elik745i/ESP-Pressure-Transducer/3D/3d_Models/cable-gland-18.snapshot.6/Screenshot 2024-12-11 at 10.22.05 AM.png

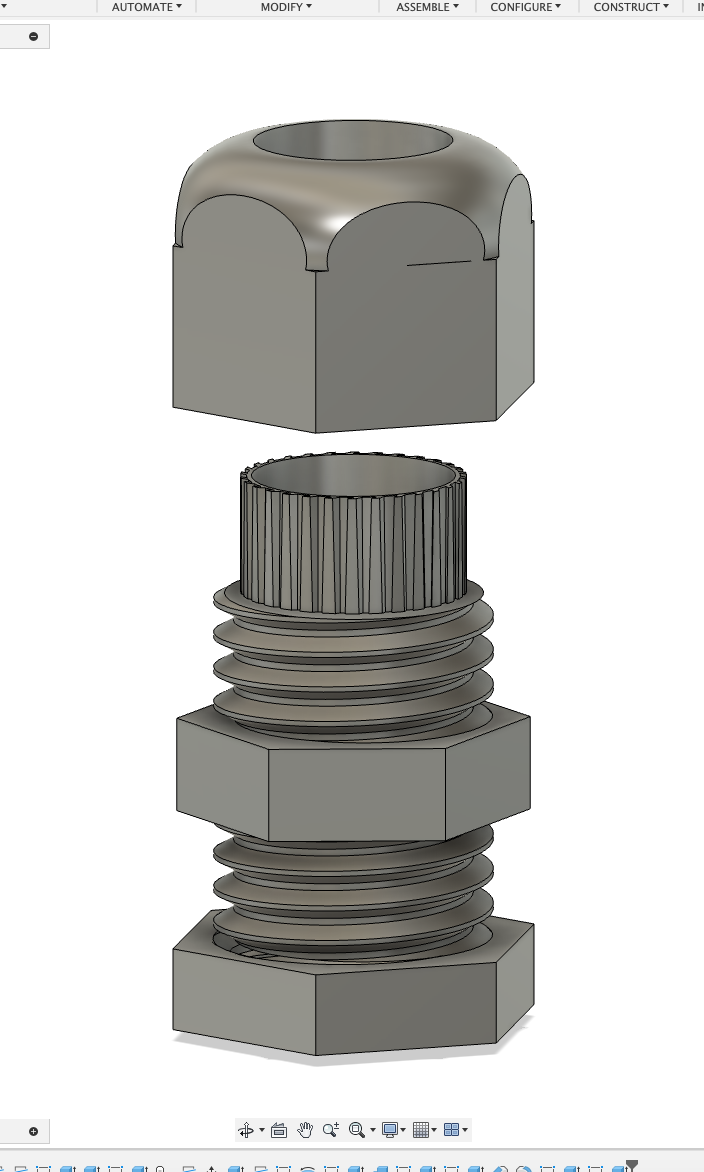
3D/3d_Models/cable-gland-18.snapshot.6/Screenshot 2024-12-11 at 10.22.05 AM.png
