elik745i/ESP-Pressure-Transducer/3D/3d_Models/mlh100pgb01a-transducer-1.snapshot.11/MLH100PGB01A.jpg

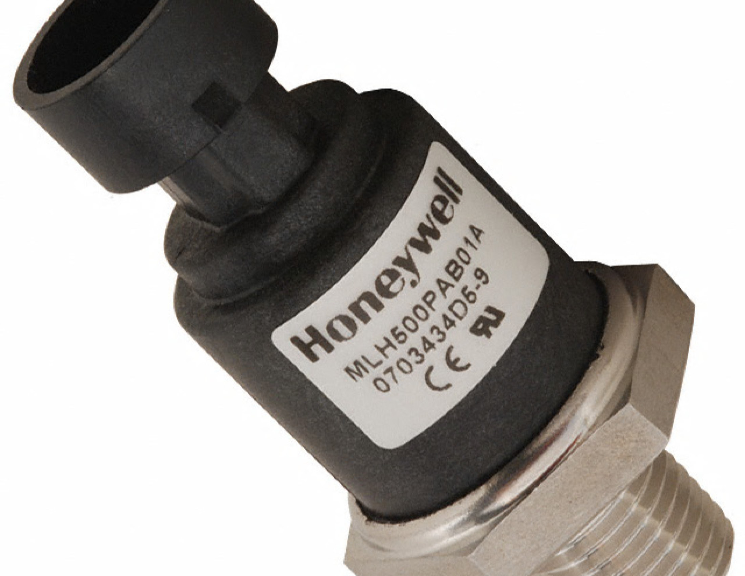
3D/3d_Models/mlh100pgb01a-transducer-1.snapshot.11/MLH100PGB01A.jpg
