elik745i/ESP-Pressure-Transducer/3D/3d_Models/polyamid-kablo-rakoru-polyamide-cable-gland-1.snapshot.6/2024-08-10_15-54-43.png

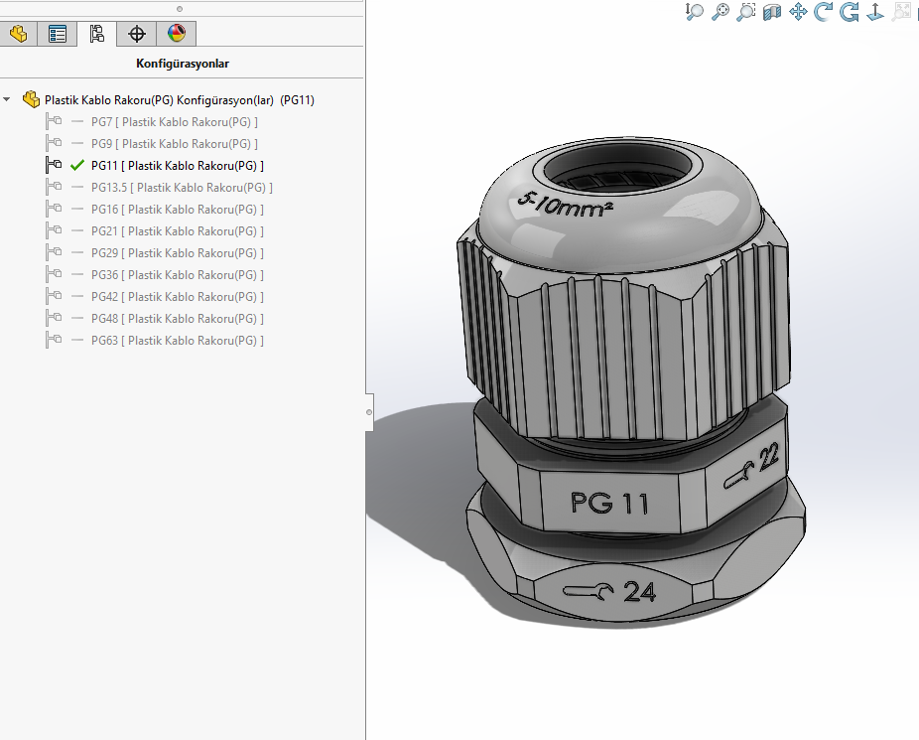
3D/3d_Models/polyamid-kablo-rakoru-polyamide-cable-gland-1.snapshot.6/2024-08-10_15-54-43.png
