elik745i/ESP-Pressure-Transducer/Docs/1.jpeg

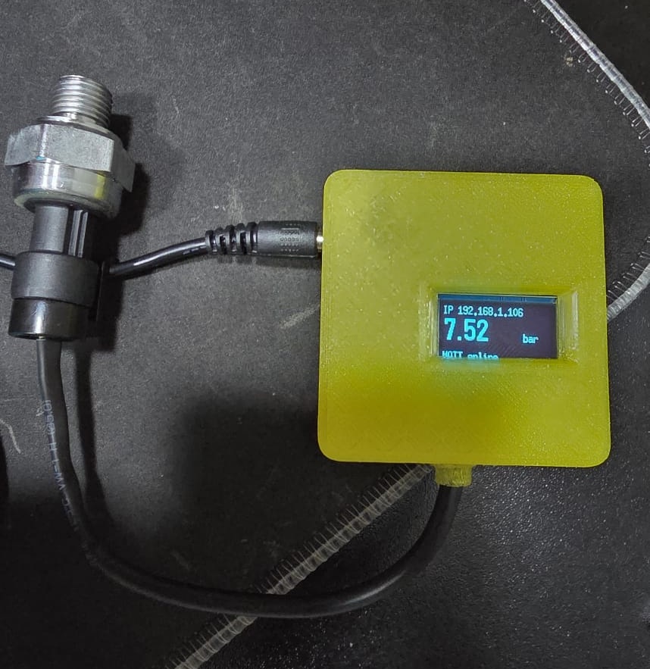
Docs/1.jpeg
