elik745i/ESP-Pressure-Transducer/Docs/2.jpeg

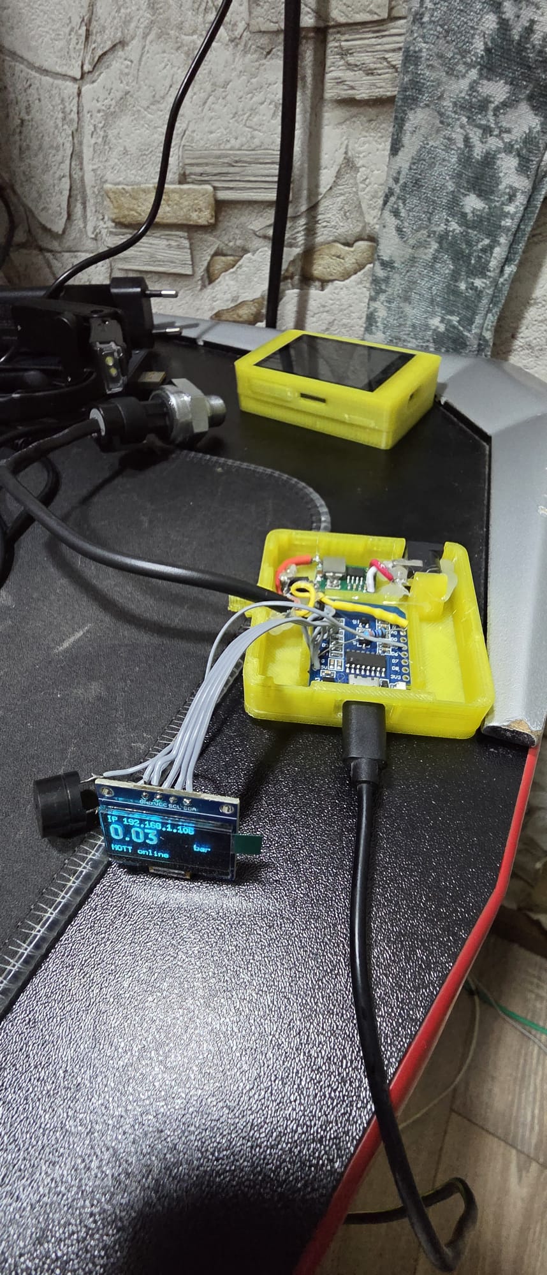
Docs/2.jpeg
