elik745i/ESP-Pressure-Transducer/Docs/3.jpeg

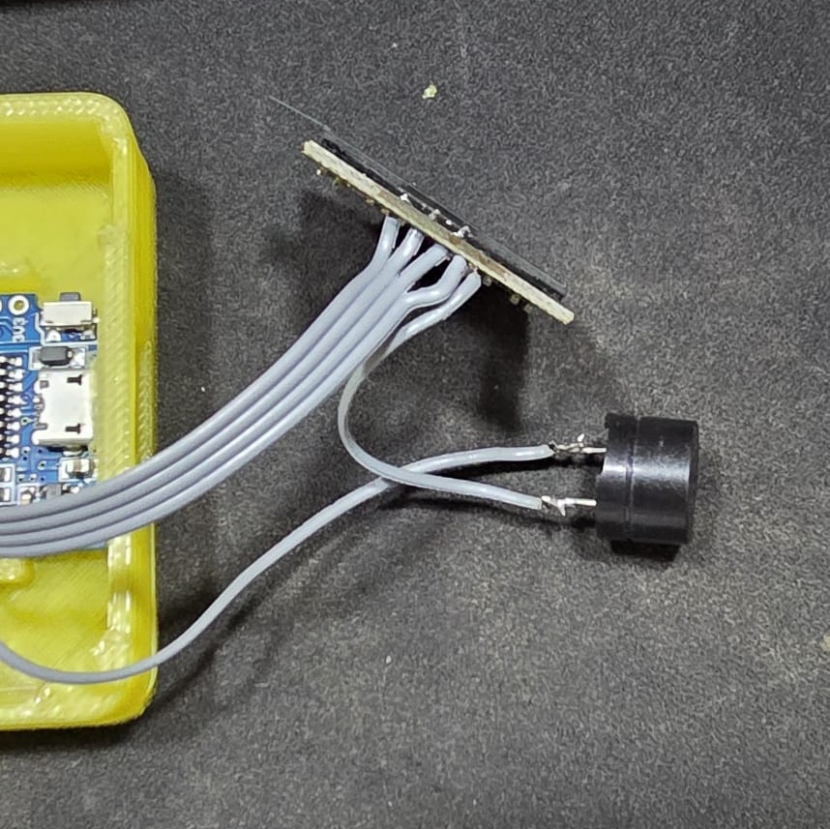
Docs/3.jpeg
