elik745i/ESP-Pressure-Transducer/Docs/4.jpeg

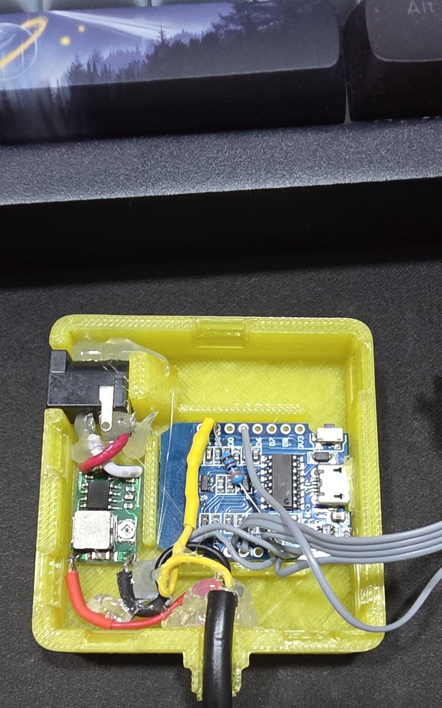
Docs/4.jpeg
