elik745i/ESP-Pressure-Transducer/Docs/botth sensors.jpg

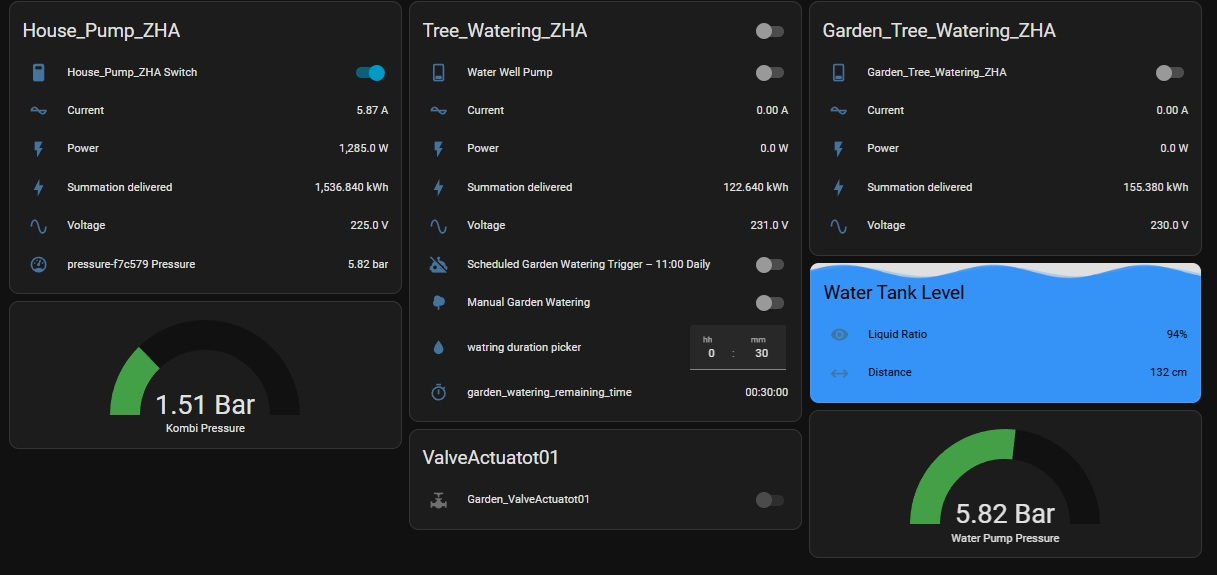
Docs/botth sensors.jpg
