elik745i/ESP-Pressure-Transducer/Docs/espo.jpeg

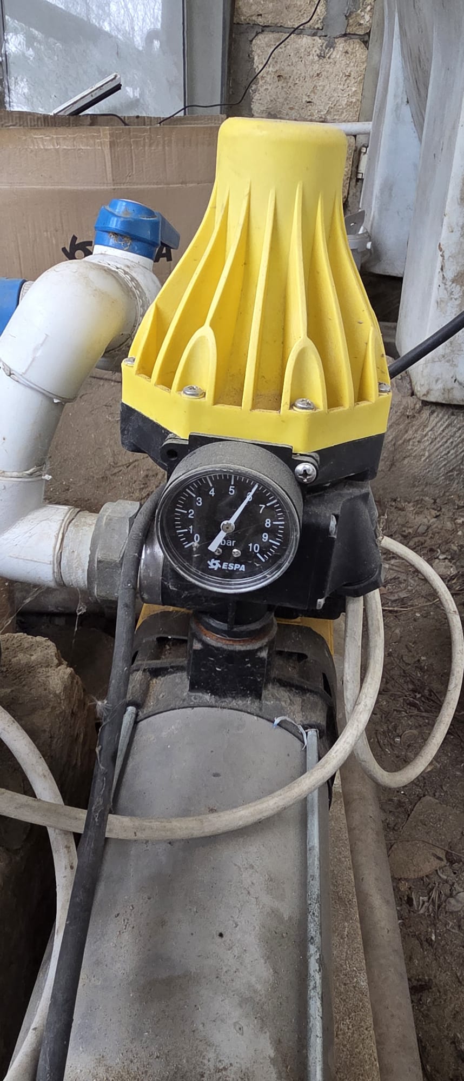
Docs/espo.jpeg
