elik745i/ESP-Pressure-Transducer/Docs/touch1.png

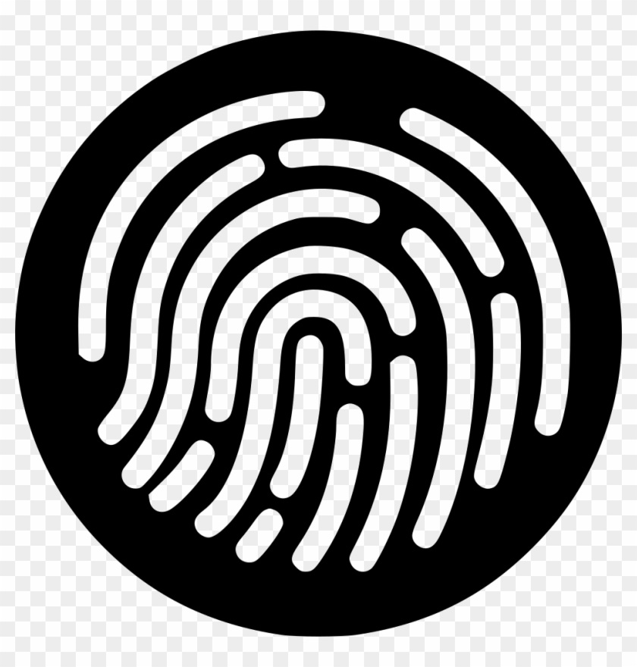
Docs/touch1.png
