elik745i/ESP-Pressure-Transducer/Docs/WhatsApp Image 2026-03-30 at 17.22.24.jpeg

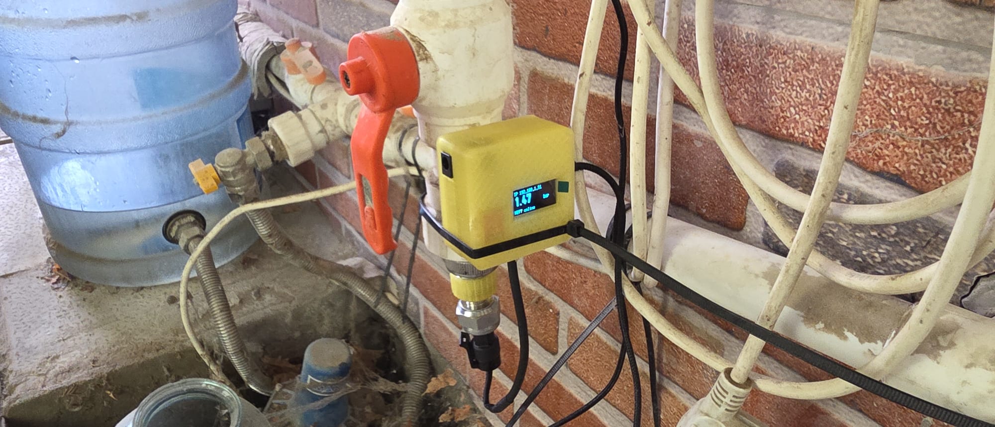
Docs/WhatsApp Image 2026-03-30 at 17.22.24.jpeg
