elik745i/ESP-Pressure-Transducer/Docs/WhatsApp Image 2026-03-30 at 17.23.52.jpeg

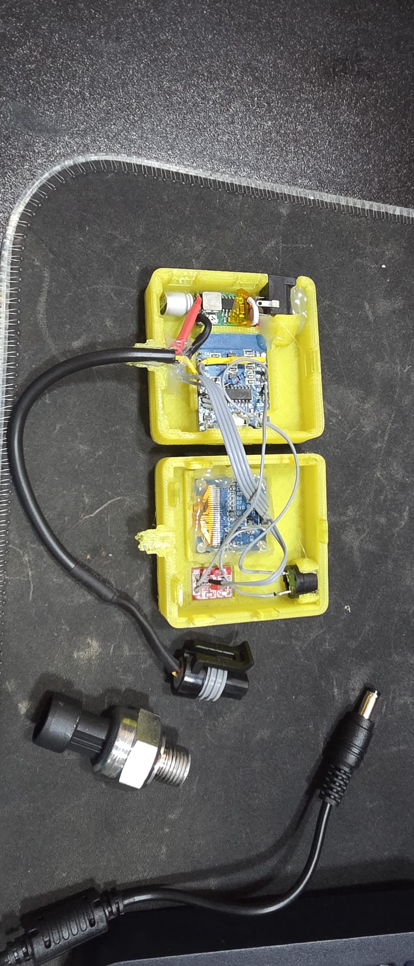
Docs/WhatsApp Image 2026-03-30 at 17.23.52.jpeg
