elik745i/ESP-Pressure-Transducer/3D/3d_Models/cable-gland-18.snapshot.6/sph17mmC.stl

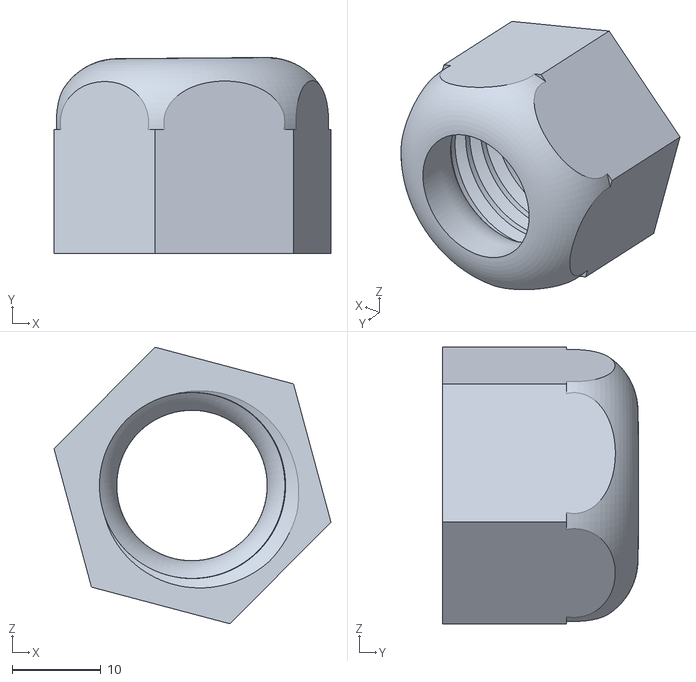
[picture p42: CAD file, 2026-03-26]
3D/3d_Models/cable-gland-18.snapshot.6/sph17mmC.stl
31.3 x 22.1 x 31.2
