elik745i/ESP-Pressure-Transducer/3D/STL/ESP_Pressure_Transsducer_bot.3mf

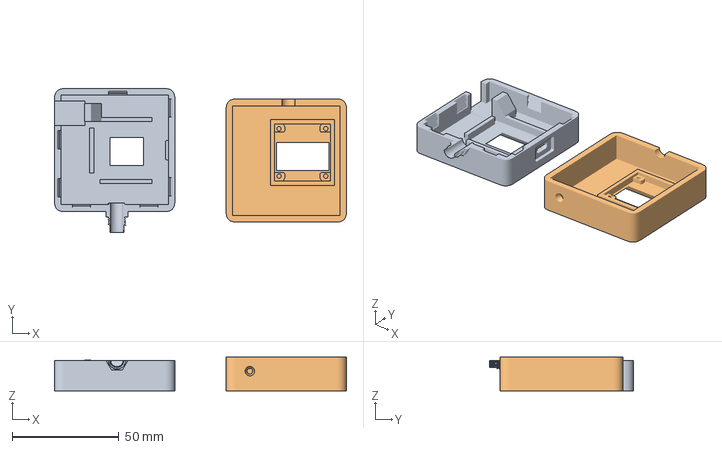
[picture p43: CAD file, 2026-03-26]
3D/STL/ESP_Pressure_Transsducer_bot.3mf
136.6 x 67.4 x 15.8 mm
ESP_Pressure_Transsducer_bot.stl
ESP_Pressure_Transsducer_top.stl
