elik745i/ESP-Pressure-Transducer/3D/STL/nut.stl

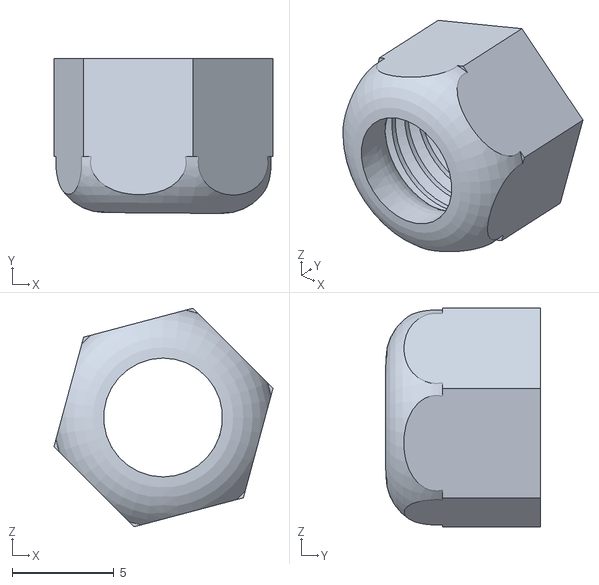
[picture p44: CAD file, 2026-03-26]
3D/STL/nut.stl
10.8 x 7.61 x 10.7
