elik745i/ESP-Pressure-Transducer/Docs/installation.jpeg

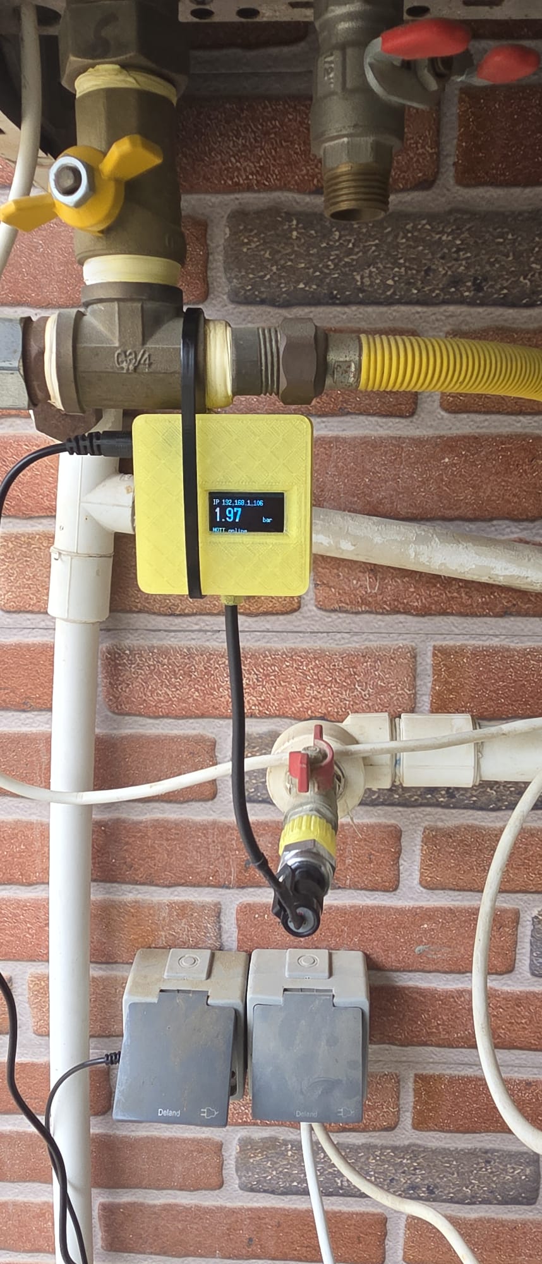
Docs/installation.jpeg
