elik745i/ESP-Pressure-Transducer/Docs/calibration.jpeg

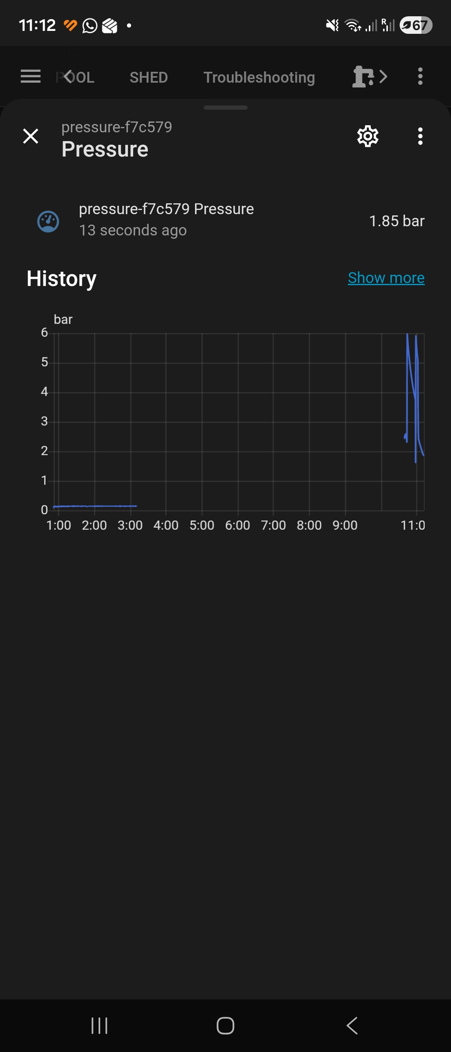
Docs/calibration.jpeg
